SolderedElectronics/IO-expander-MCP23017-breakout-hardware-design/OUTPUTS/V1.3.0/IO expander MCP23017 breakout Pinout.png

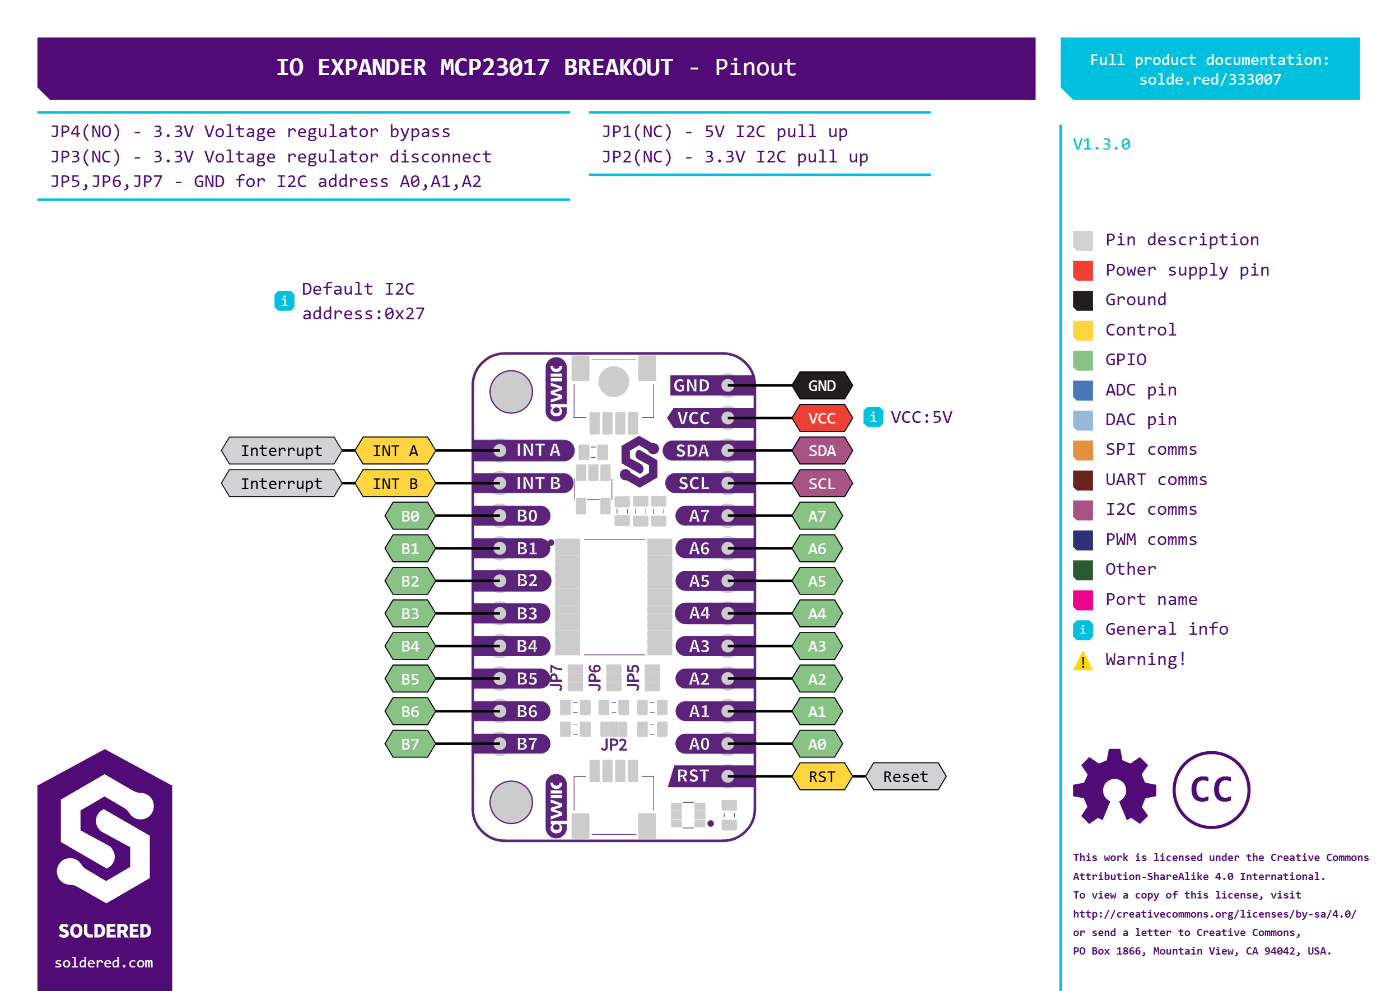
OUTPUTS/V1.3.0/IO expander MCP23017 breakout Pinout.png
